ramonsnchz/Haptic-Modules/Twister Files/CADs/springTwister_tactor.SLDPRT

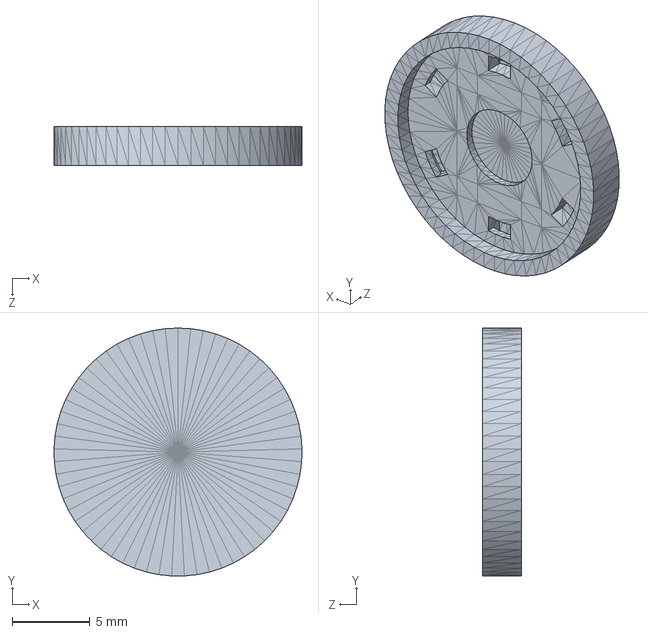
[picture p15: CAD file, 2021-05-06]
Twister Files/CADs/springTwister_tactor.SLDPRT
16.0 x 16.0 x 2.50 mm
