ramonsnchz/Haptic-Modules/Slider Files/CADs/Slider.SLDPRT

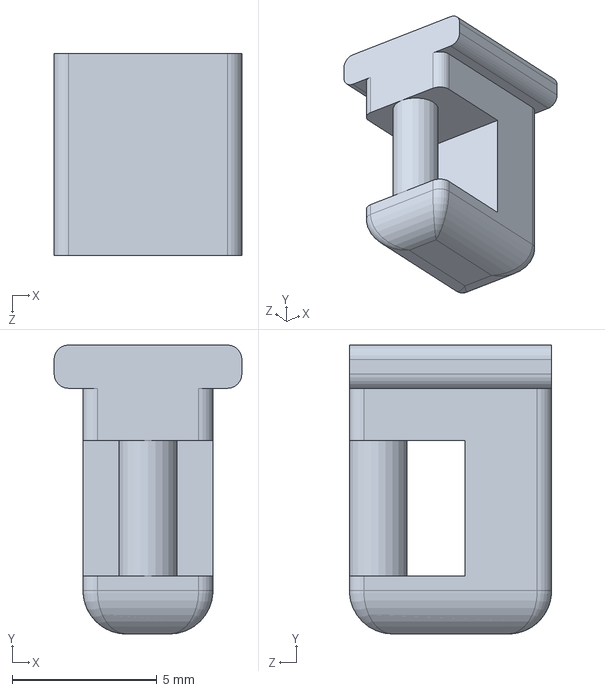
[picture p16: CAD file, 2021-05-03]
Slider Files/CADs/Slider.SLDPRT
6.50 x 10.0 x 7.00 mm
