ramonsnchz/Haptic-Modules/Slider Files/CADs/Arm.SLDPRT

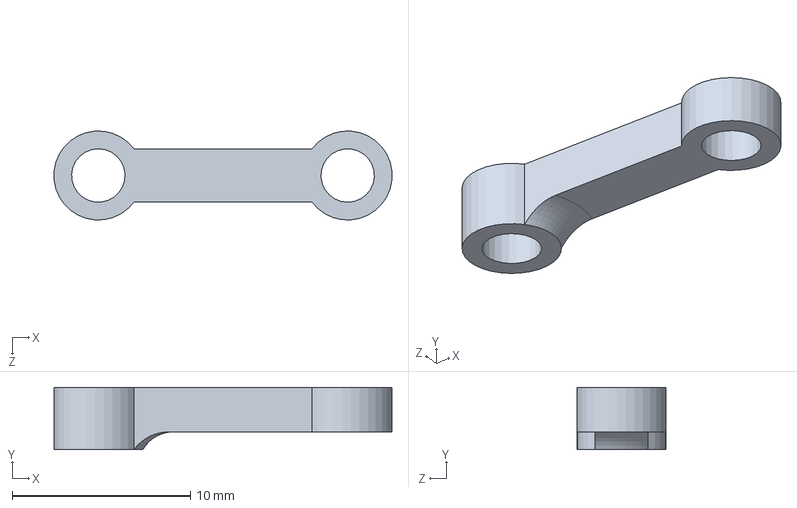
[picture p17: CAD file, 2021-05-03]
Slider Files/CADs/Arm.SLDPRT
19.0 x 3.50 x 4.99 mm
